iliasam/OpenLIDAR/PCB/3D_view1.png

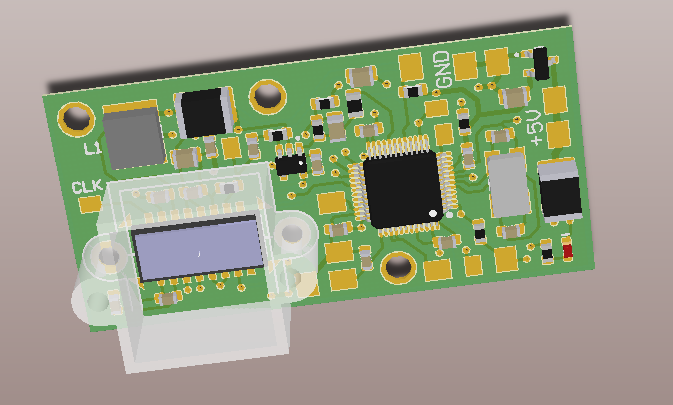
PCB/3D_view1.png
