iliasam/OpenLIDAR/PCB/3D_view2.png

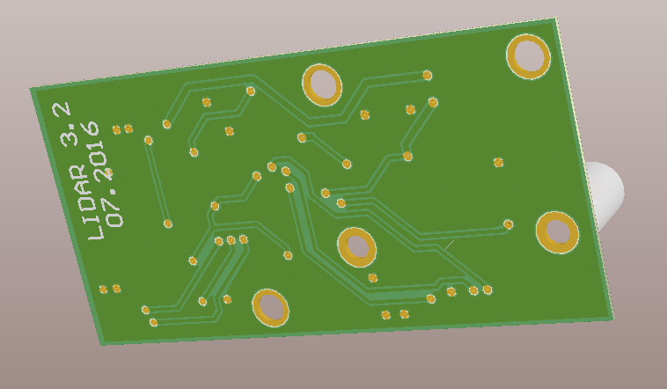
PCB/3D_view2.png
