iliasam/OpenLIDAR/ROS/hector_slam_map_example.png

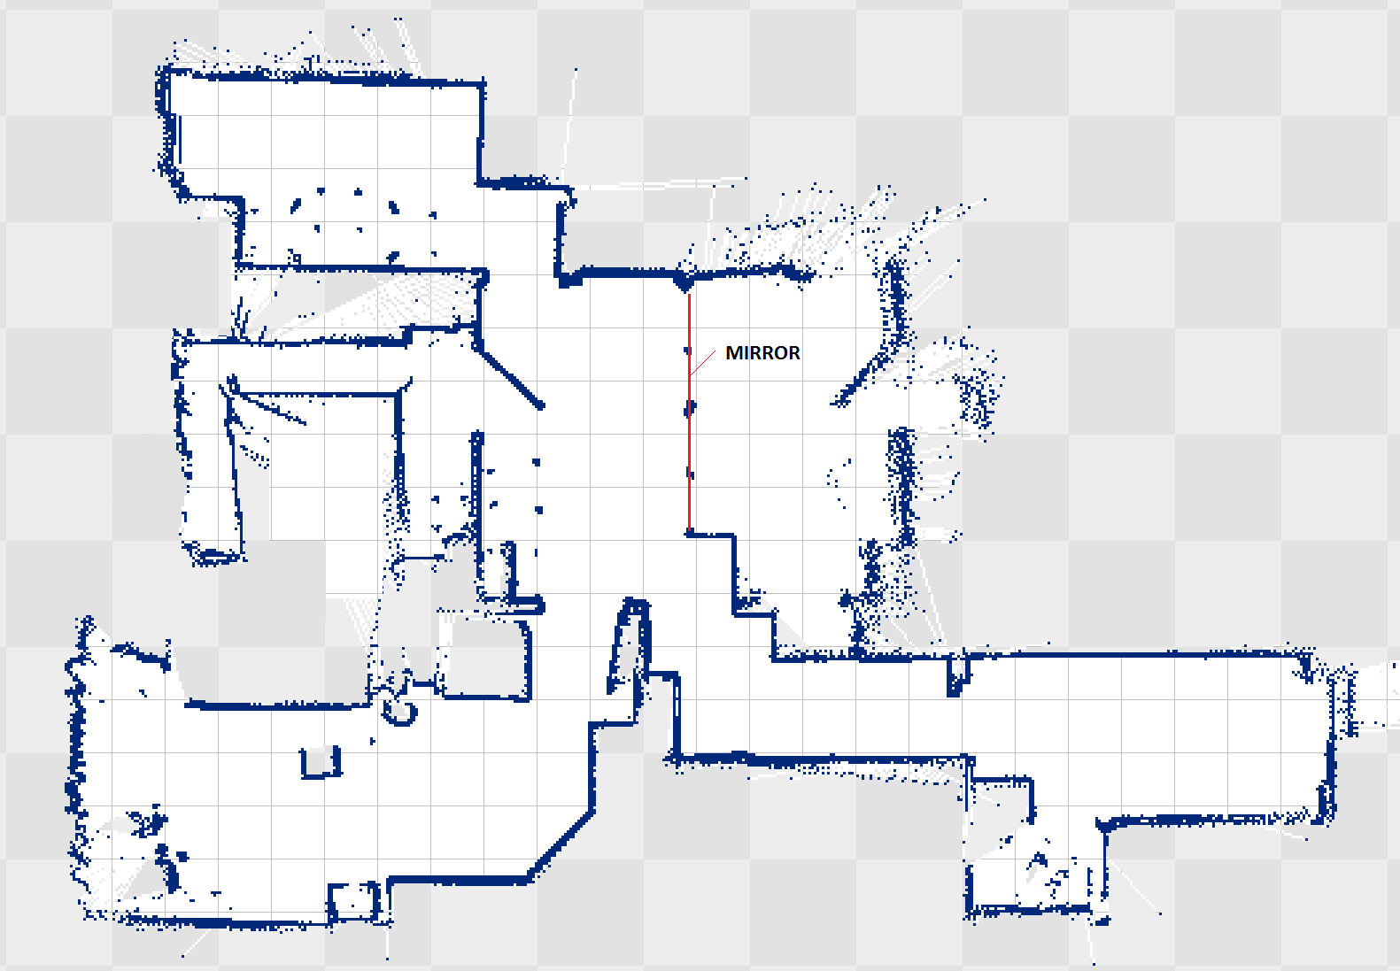
ROS/hector_slam_map_example.png
