iliasam/OpenLIDAR/wiki_images/mirror_image.png

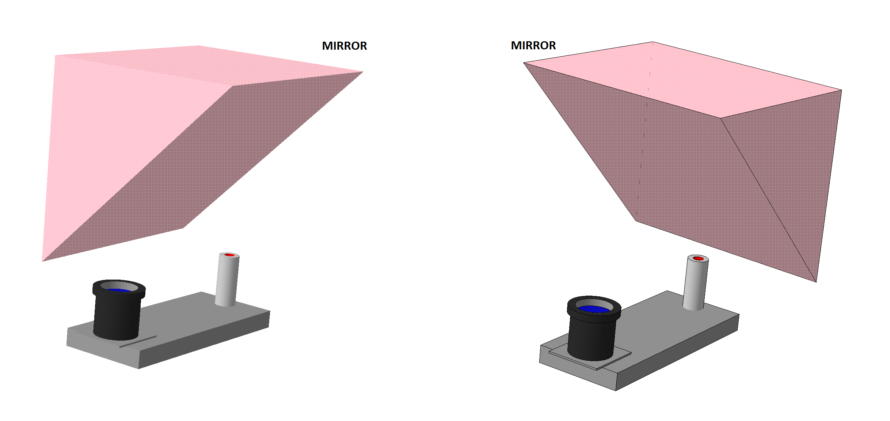
wiki_images/mirror_image.png
