iliasam/OpenLIDAR/3D_models/build2a.png

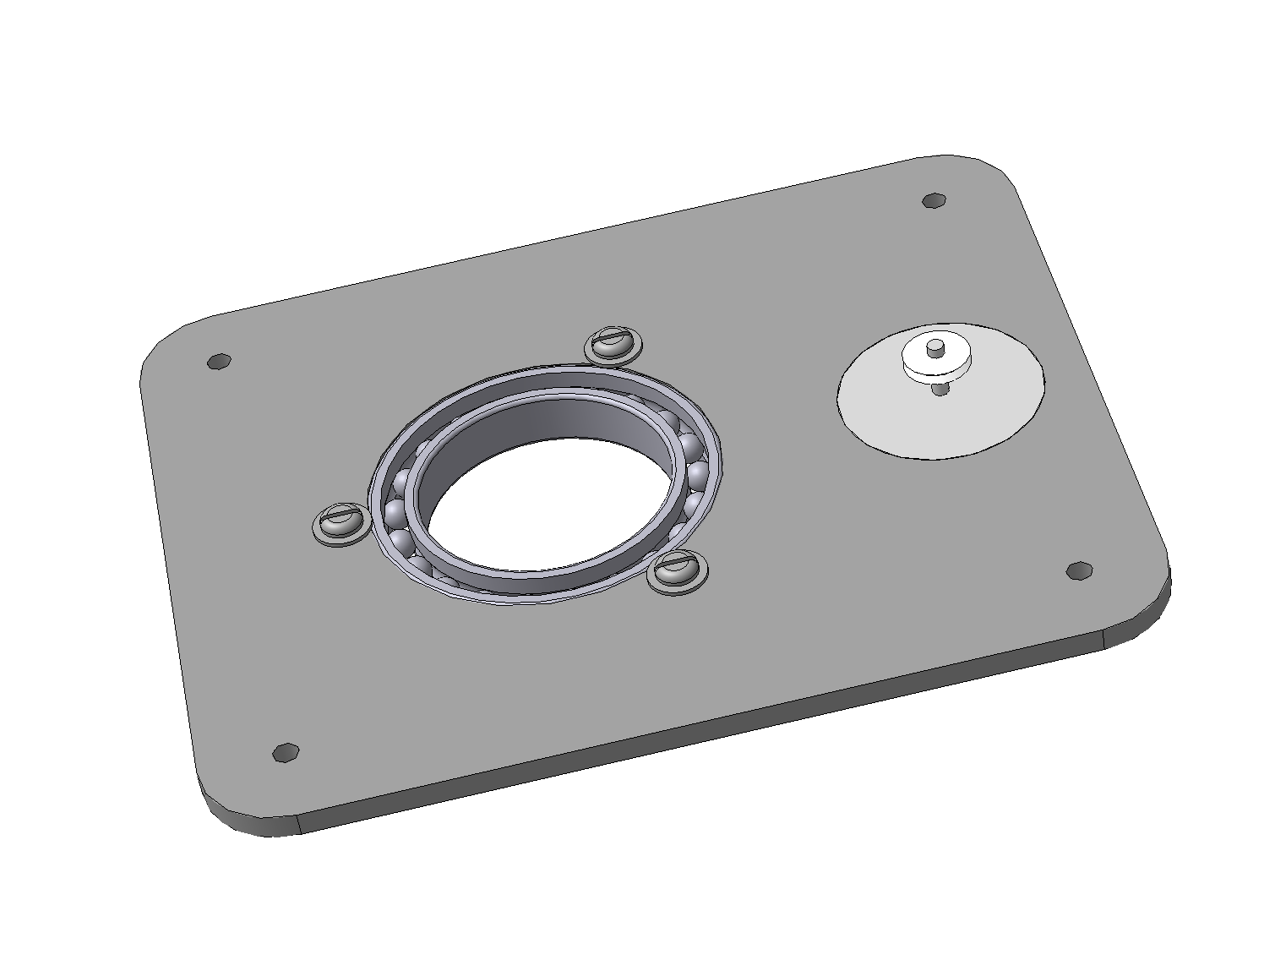
3D_models/build2a.png
