iliasam/OpenLIDAR/3D_models/build2c.png

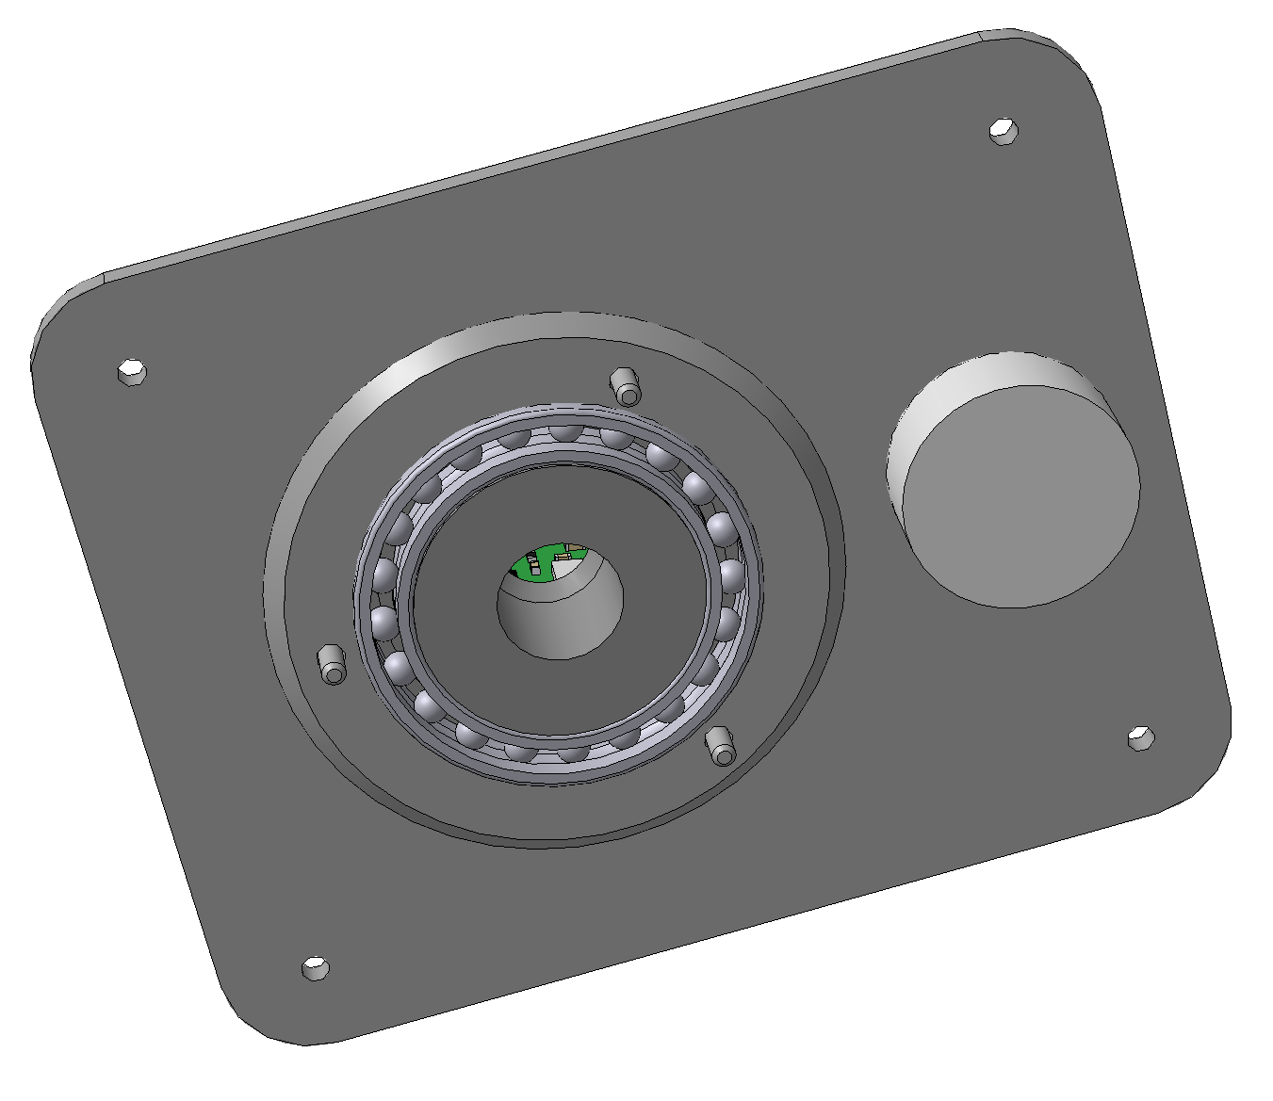
3D_models/build2c.png
