iliasam/OpenLIDAR/3D_models/build2f.png

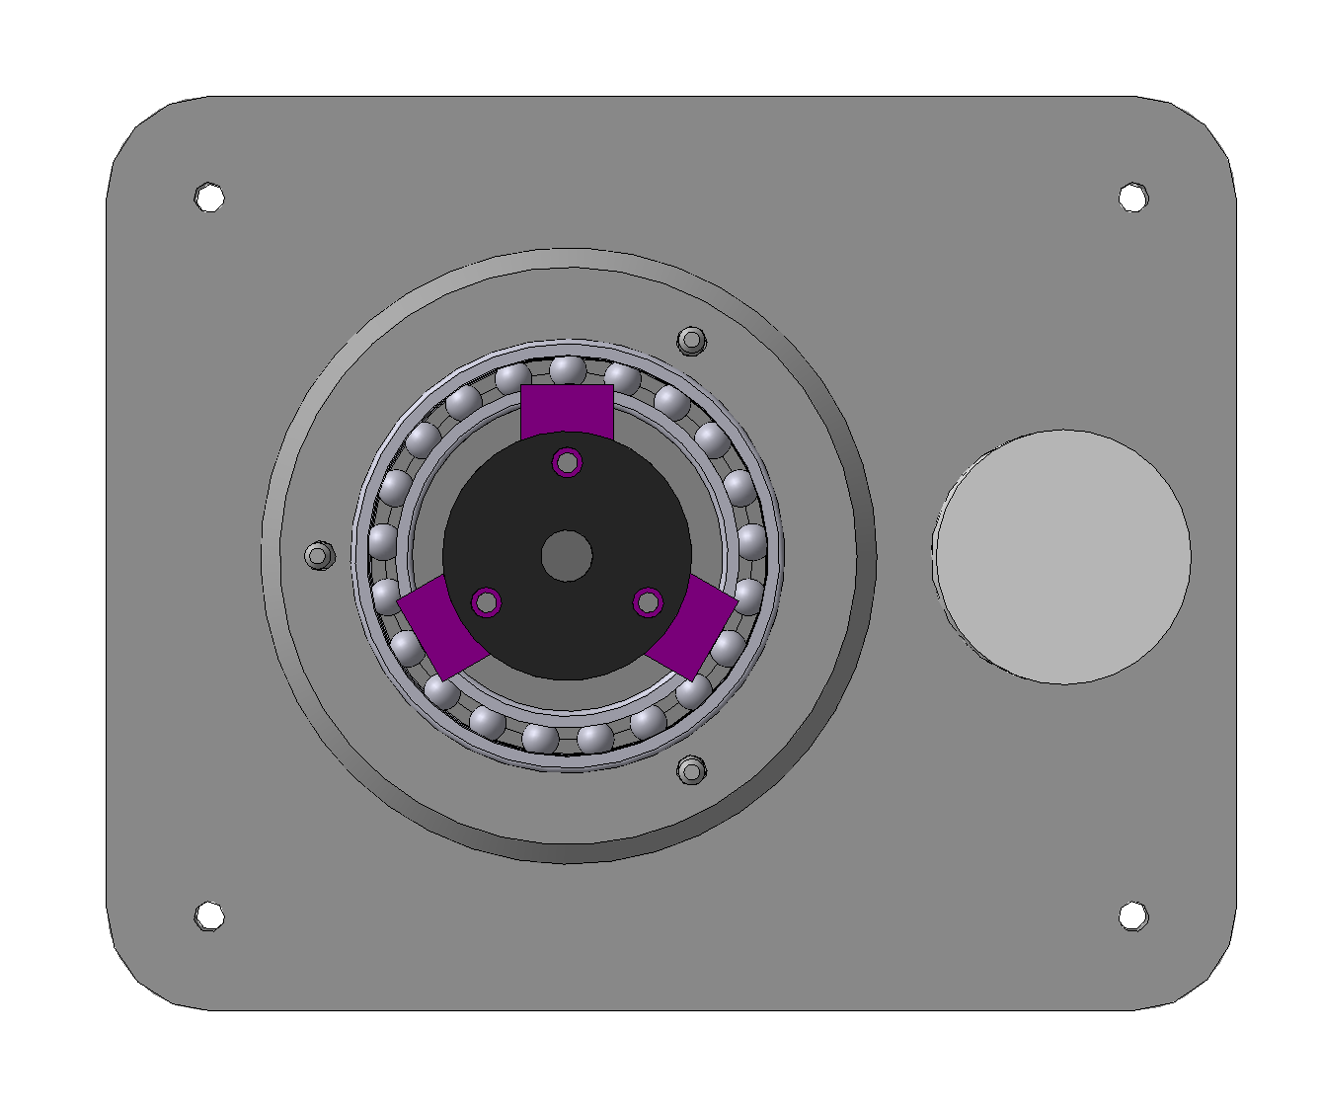
3D_models/build2f.png
