iliasam/OpenLIDAR/3D_models/build_disk_01b.png

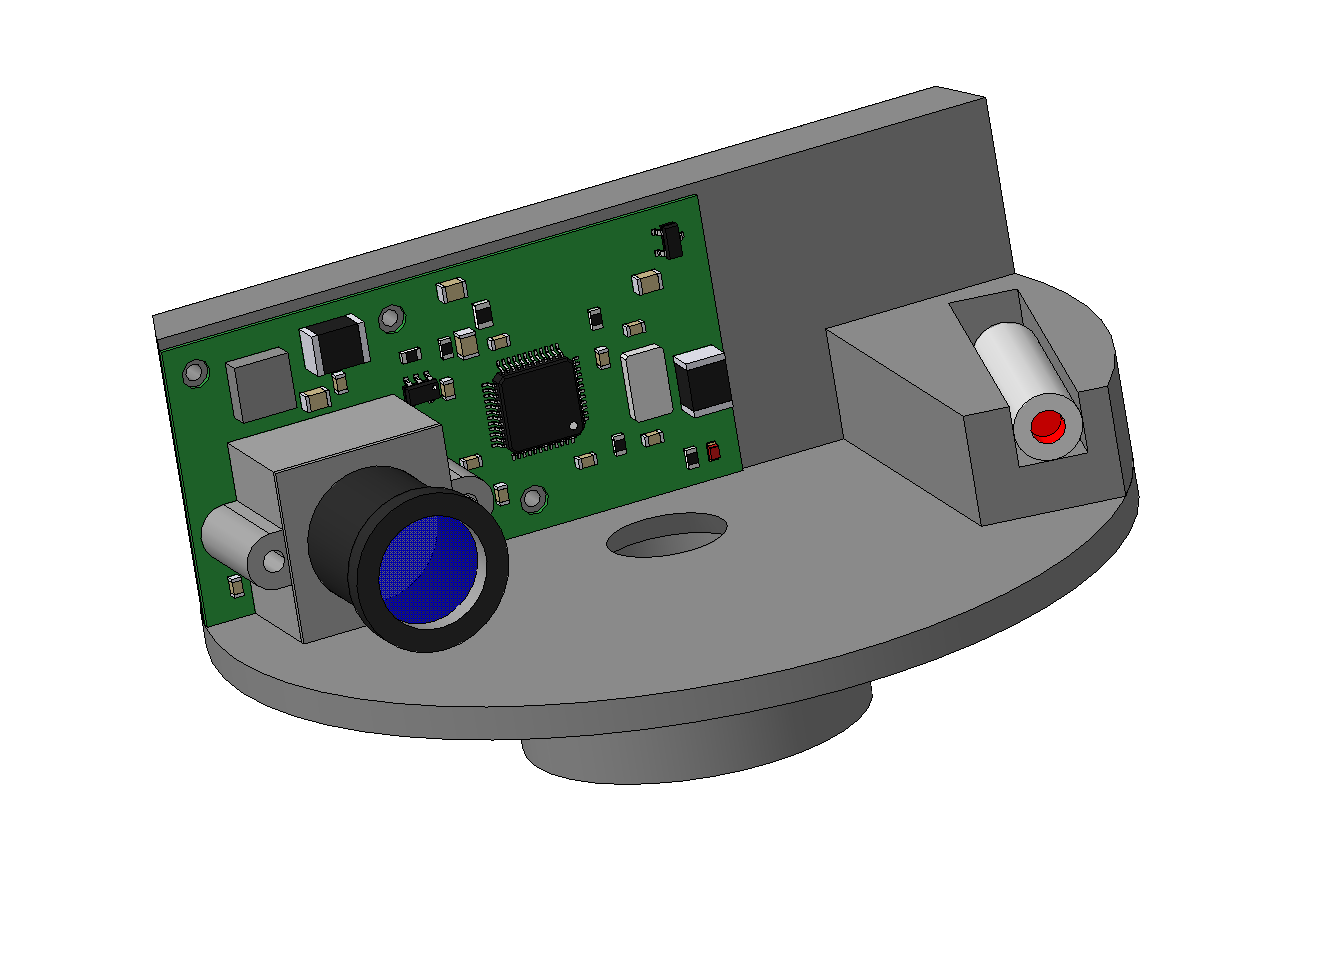
3D_models/build_disk_01b.png
