iliasam/OpenLIDAR/3D_models/build_disk_01c.png

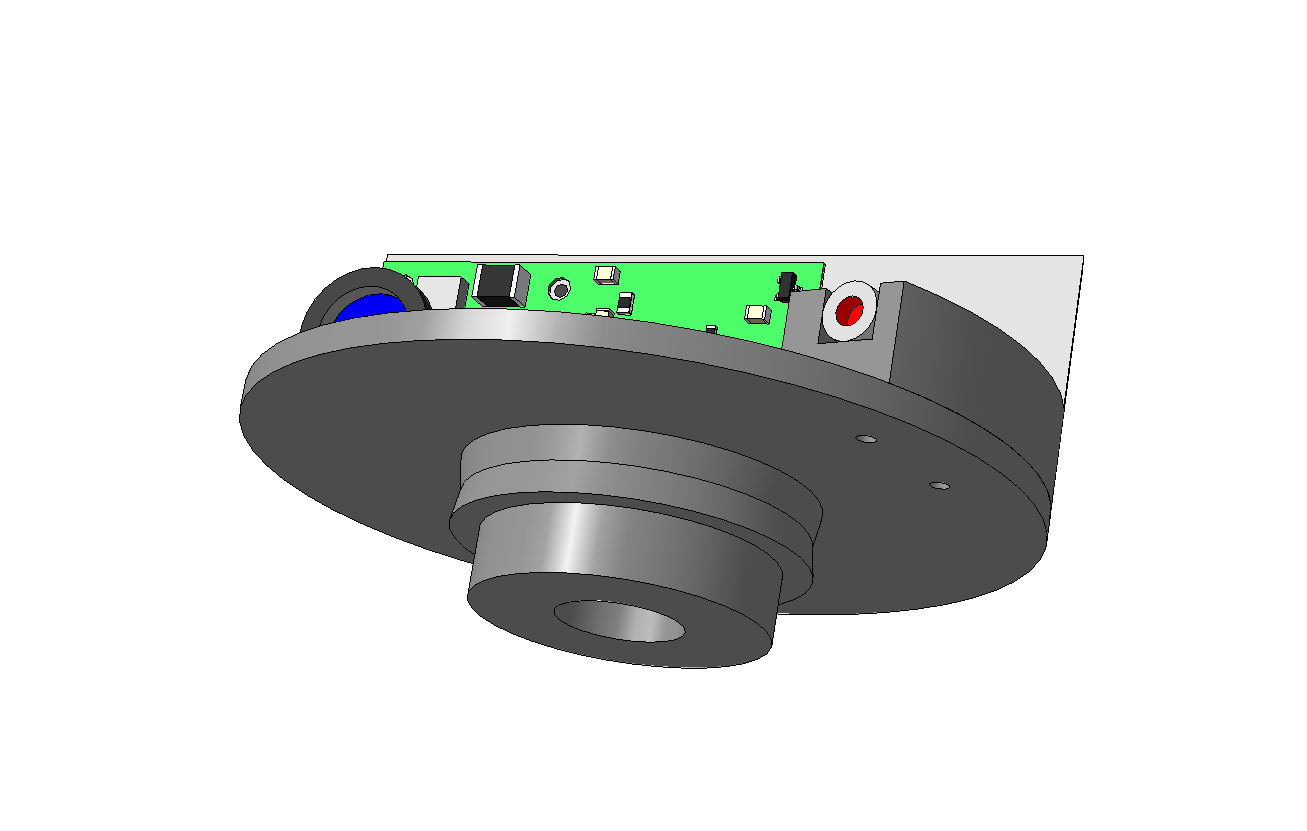
3D_models/build_disk_01c.png
