iliasam/OpenLIDAR/PCB/assembly.png

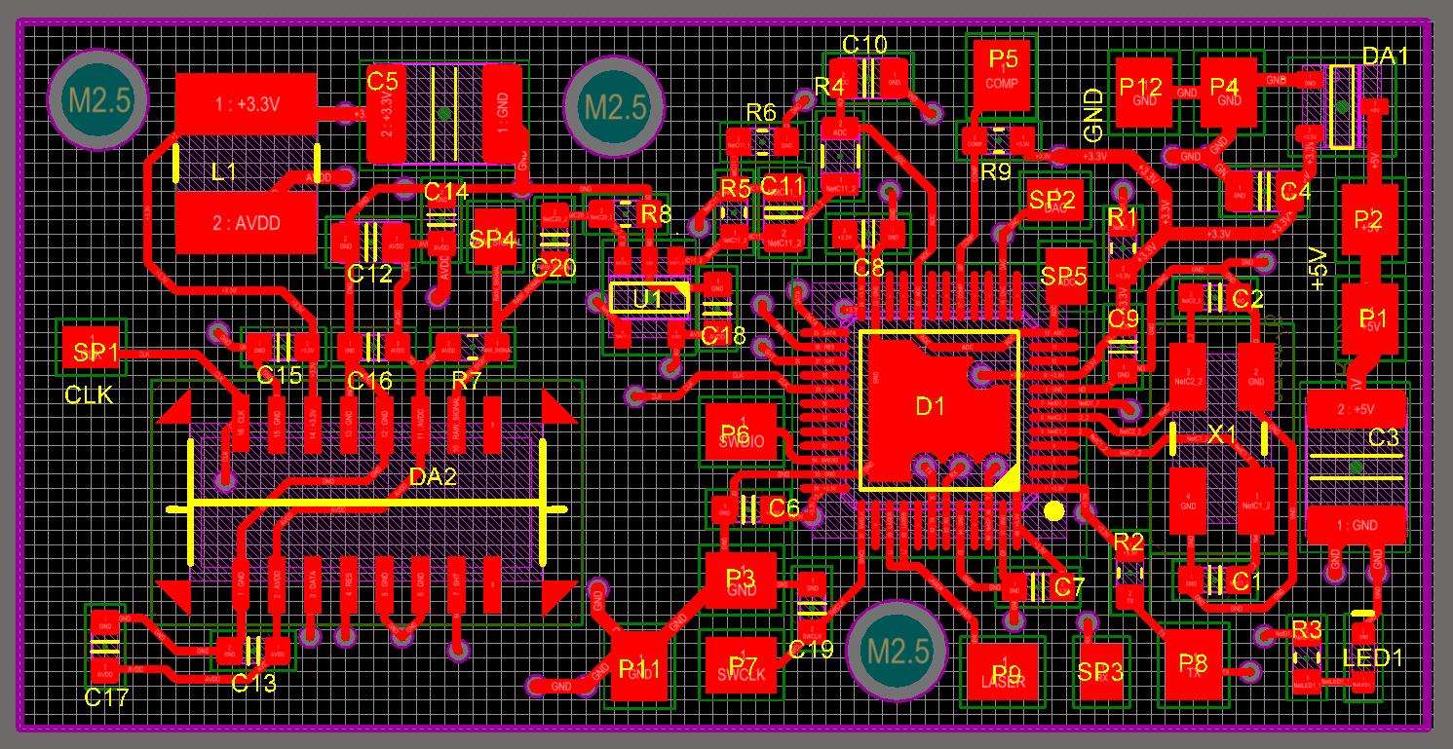
PCB/assembly.png
