iliasam/OpenLIDAR/Firmware/lidar3_image/adc_control.h

#ifndef __ADC_CONTROL_H
#define __ADC_CONTROL_H

#define LINE_BUFFER_SIZE (uint16_t)1024

void init_clk(void);
void adc_init(void);
void init_timer1(void);

void stop_capture(void);
void start_capture(void);

void capture_dma_start(void);

void start_clk_timer(void);
void init_capture_gpio(void);

void create_start_pulse(void);



#endif 
